Scyllinice/Game-Genie-Toploader-Adapter/mech/render_back.png

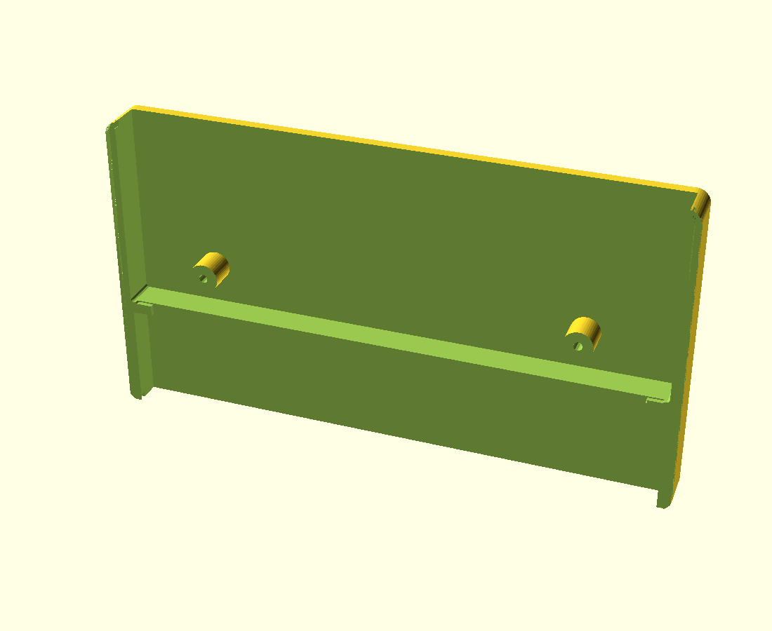
mech/render_back.png
